farhanwadia/EEGClassification/Nov 2020 Filtered Data/5s/Images/Full Length FFTs/SD_T1 Open (valve) - FFT.png

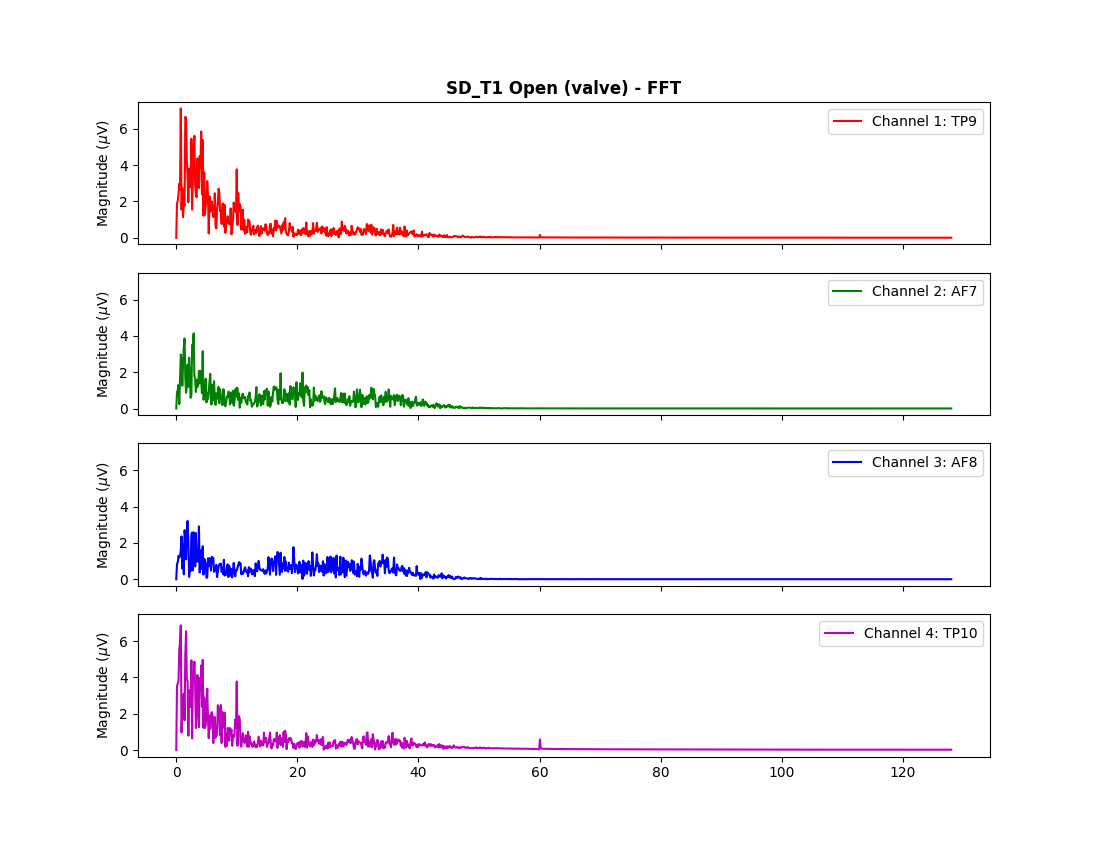
Nov 2020 Filtered Data/5s/Images/Full Length FFTs/SD_T1 Open (valve) - FFT.png
