farhanwadia/EEGClassification/Nov 2020 Filtered Data/5s/Images/Full Length FFTs/SD_T60 Close (valve) - FFT.png

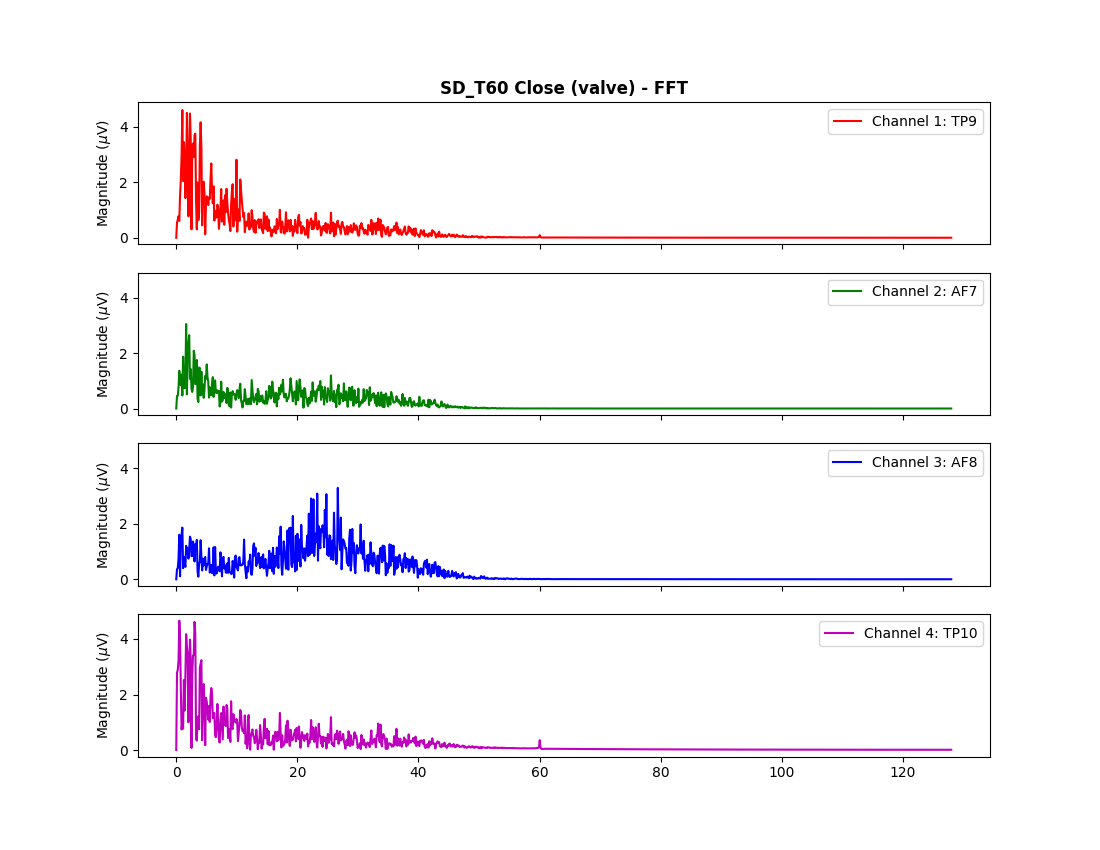
Nov 2020 Filtered Data/5s/Images/Full Length FFTs/SD_T60 Close (valve) - FFT.png
