farhanwadia/EEGClassification/Nov 2020 Filtered Data/5s/Images/ICA Images/AZ_T10 Open (valve) ICA.png

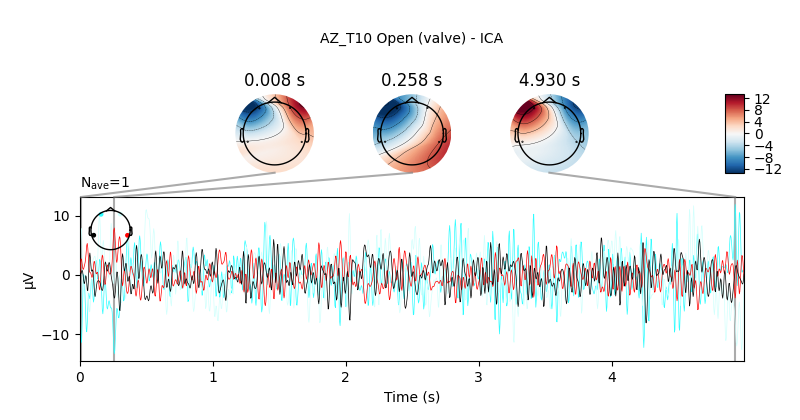
Nov 2020 Filtered Data/5s/Images/ICA Images/AZ_T10 Open (valve) ICA.png
