farhanwadia/EEGClassification/Nov 2020 Filtered Data/5s/Images/ICA Images/AZ_T17 Close (valve) ICA.png

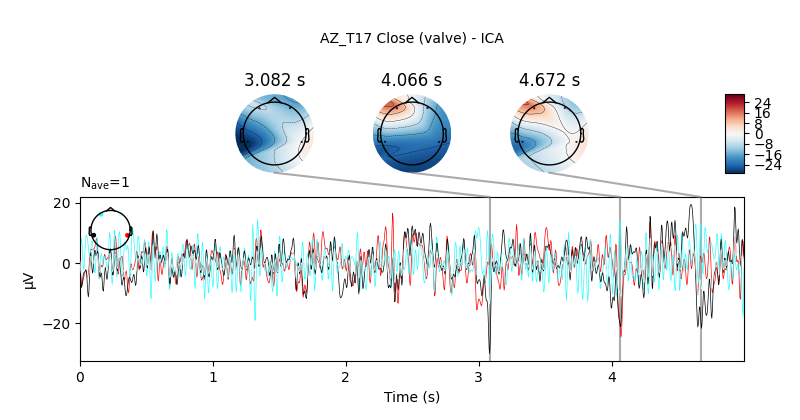
Nov 2020 Filtered Data/5s/Images/ICA Images/AZ_T17 Close (valve) ICA.png
