farhanwadia/EEGClassification/Nov 2020 Filtered Data/5s/Images/ICA Images/CJ_T1 Open (valve) ICA.png

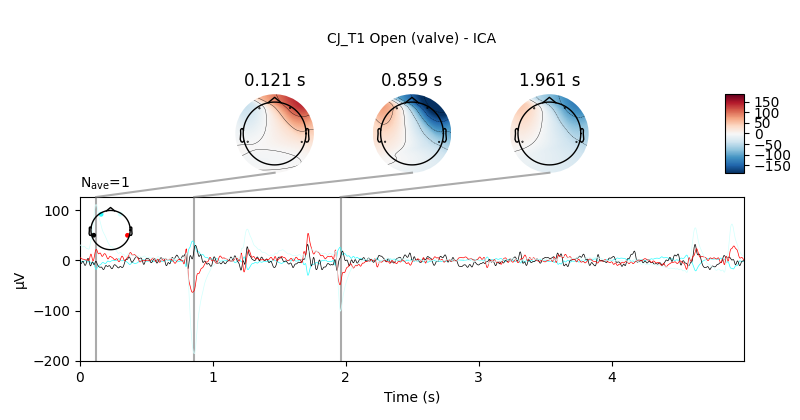
Nov 2020 Filtered Data/5s/Images/ICA Images/CJ_T1 Open (valve) ICA.png
