farhanwadia/EEGClassification/Nov 2020 Filtered Data/5s/Images/ICA Images/CJ_T15 Close (valve) ICA.png

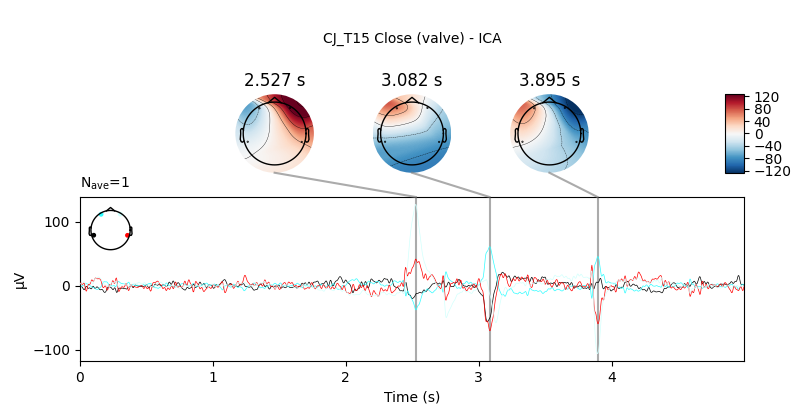
Nov 2020 Filtered Data/5s/Images/ICA Images/CJ_T15 Close (valve) ICA.png
