farhanwadia/EEGClassification/Nov 2020 Filtered Data/5s/Images/ICA Images/FW_T46 Close (valve) ICA.png

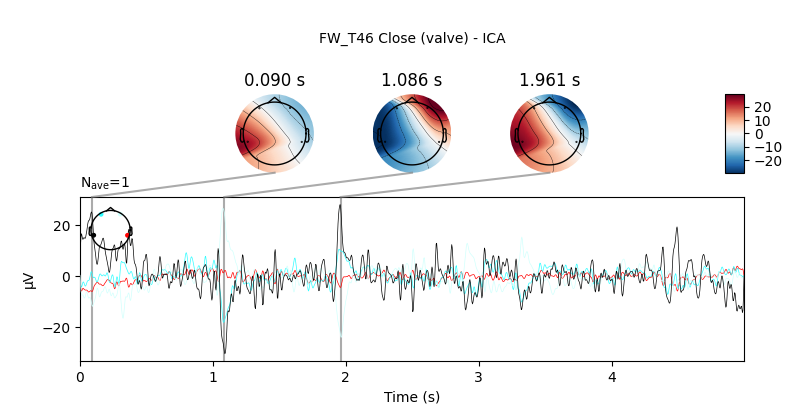
Nov 2020 Filtered Data/5s/Images/ICA Images/FW_T46 Close (valve) ICA.png
