farhanwadia/EEGClassification/Nov 2020 Filtered Data/5s/Images/ICA Images/FW_T76 Close (valve) ICA.png

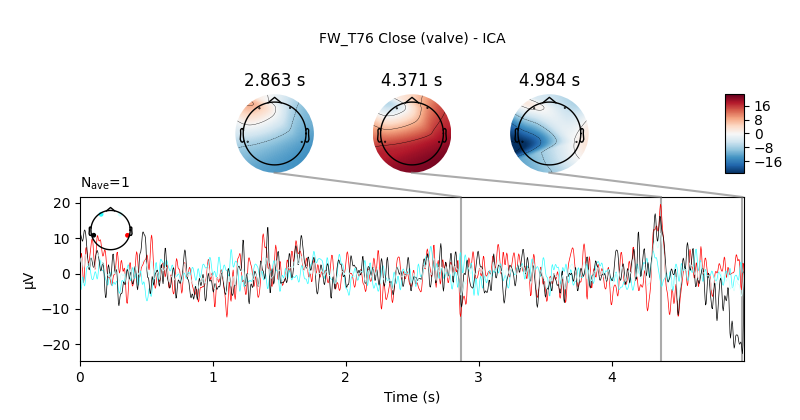
Nov 2020 Filtered Data/5s/Images/ICA Images/FW_T76 Close (valve) ICA.png
