farhanwadia/EEGClassification/Nov 2020 Filtered Data/5s/Images/ICA Images/SD_T7 Open (valve)_(2) ICA.png

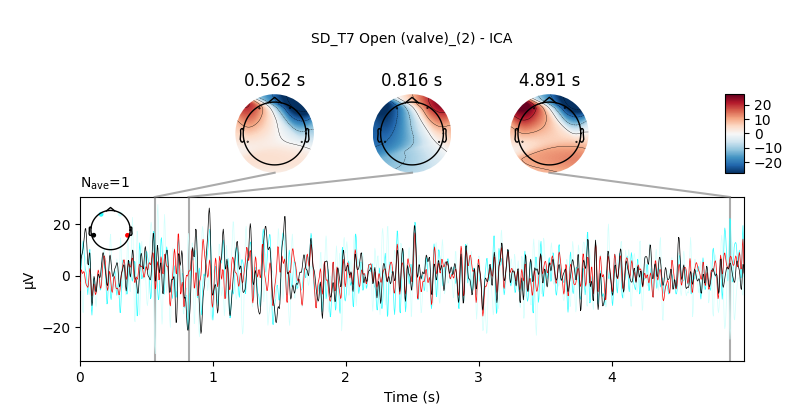
Nov 2020 Filtered Data/5s/Images/ICA Images/SD_T7 Open (valve)_(2) ICA.png
