farhanwadia/EEGClassification/Nov 2020 Filtered Data/5s/Images/ICA Images/SD_T11 Close (valve)_(1) ICA.png

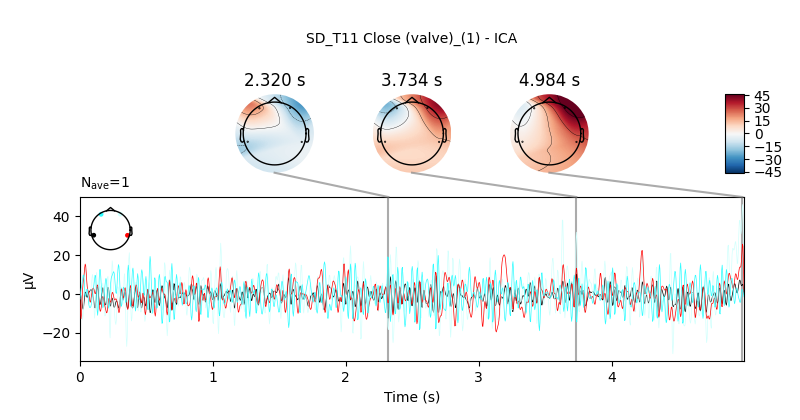
Nov 2020 Filtered Data/5s/Images/ICA Images/SD_T11 Close (valve)_(1) ICA.png
