farhanwadia/EEGClassification/Nov 2020 Filtered Data/5s/Images/ICA Images/SD_T21 Open (valve) ICA.png

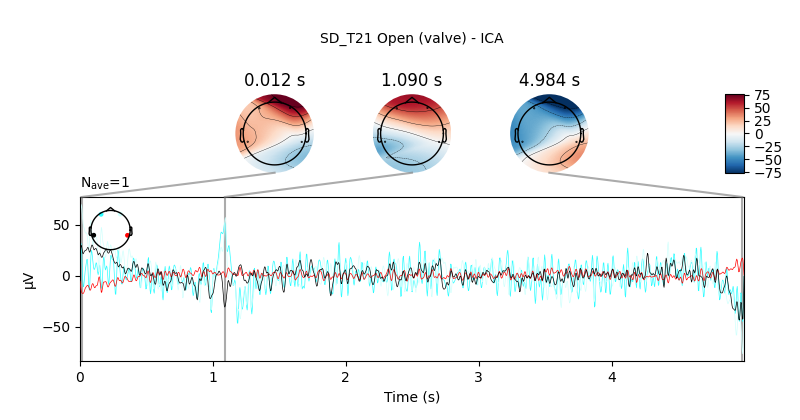
Nov 2020 Filtered Data/5s/Images/ICA Images/SD_T21 Open (valve) ICA.png
