farhanwadia/EEGClassification/Nov 2020 Filtered Data/5s/Images/ICA Images/SD_T22 Close (valve) ICA.png

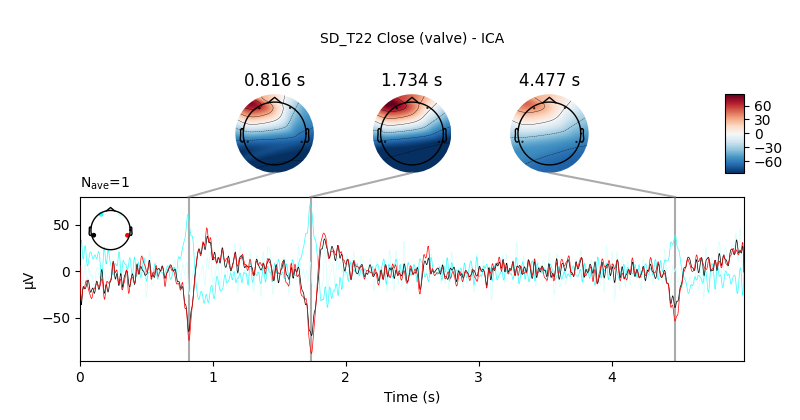
Nov 2020 Filtered Data/5s/Images/ICA Images/SD_T22 Close (valve) ICA.png
