farhanwadia/EEGClassification/Nov 2020 Filtered Data/5s/Images/ICA Images/SD_T28 Close (valve) ICA.png

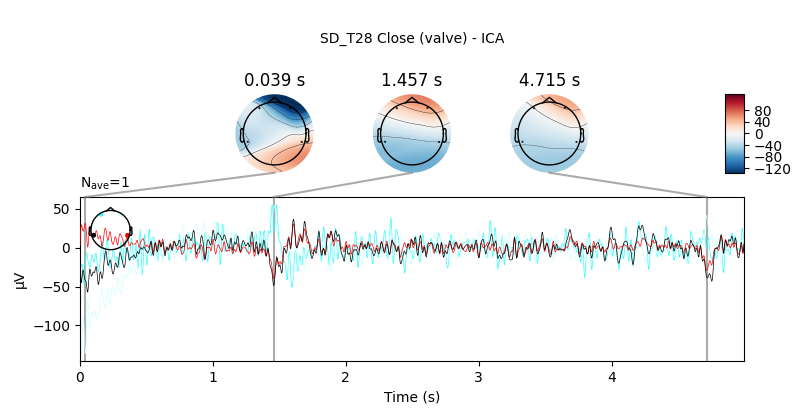
Nov 2020 Filtered Data/5s/Images/ICA Images/SD_T28 Close (valve) ICA.png
