farhanwadia/EEGClassification/Prototype and Final Design CAD Assemblies/Parts/Power Diode 1N4001.step

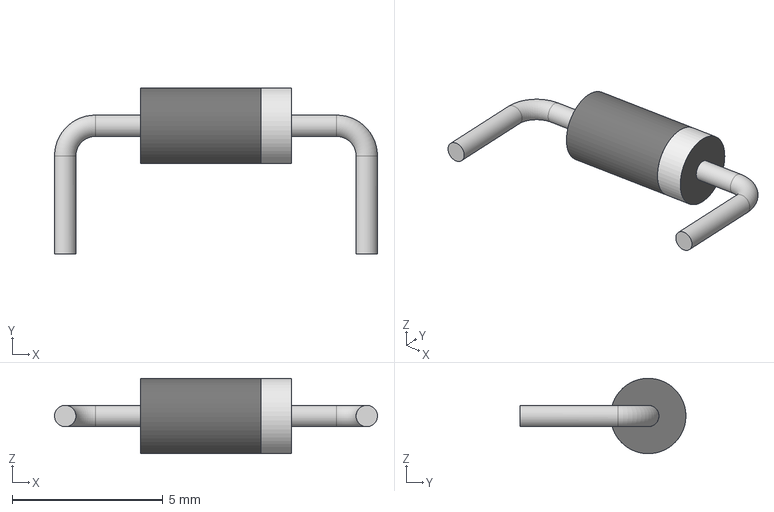
[picture p157: CAD file, 2021-03-26]
Prototype and Final Design CAD Assemblies/Parts/Power Diode 1N4001.step
10.7 x 5.50 x 2.50 mm
