farhanwadia/EEGClassification/Prototype and Final Design CAD Assemblies/Parts/Solenoid.SLDPRT

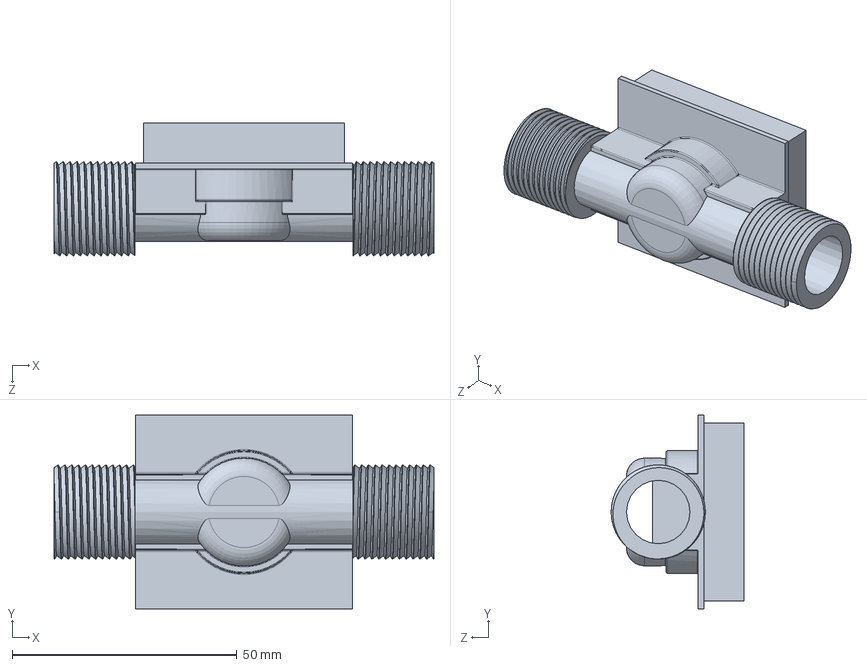
[picture p158: CAD file, 2021-03-26]
Prototype and Final Design CAD Assemblies/Parts/Solenoid.SLDPRT
84.6 x 43.2 x 29.5 mm
