farhanwadia/EEGClassification/Prototype and Final Design CAD Assemblies/Parts/cylinder.SLDPRT

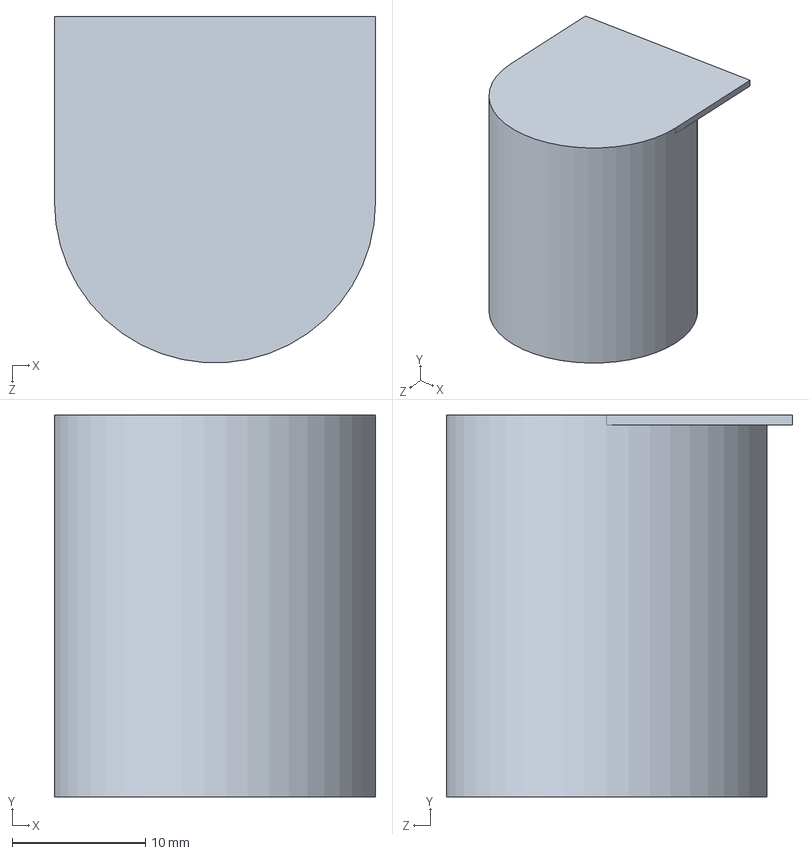
[picture p159: CAD file, 2021-03-26]
Prototype and Final Design CAD Assemblies/Parts/cylinder.SLDPRT
24.1 x 28.7 x 26.0 mm
