farhanwadia/EEGClassification/Prototype and Final Design CAD Assemblies/Parts/LEAD.SLDPRT

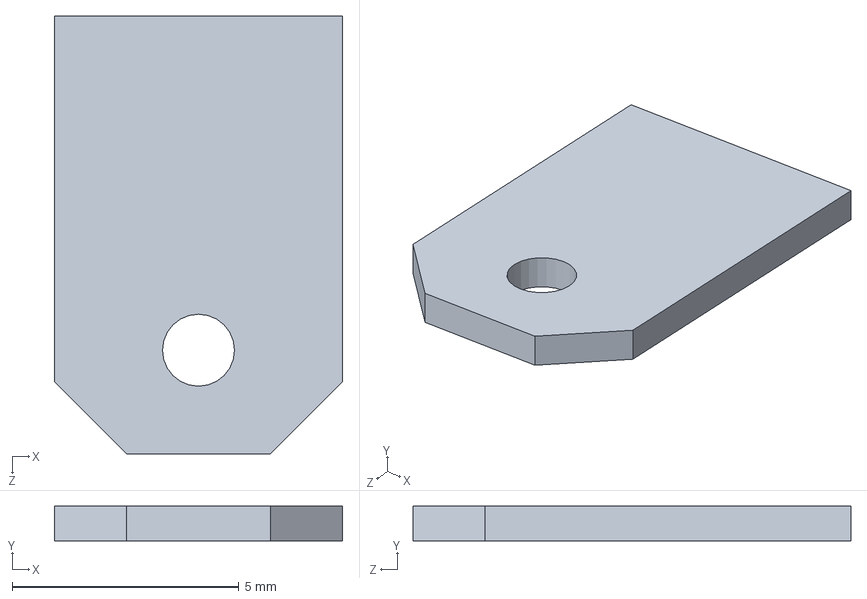
[picture p160: CAD file, 2021-03-26]
Prototype and Final Design CAD Assemblies/Parts/LEAD.SLDPRT
6.35 x 0.762 x 9.65 mm
