farhanwadia/EEGClassification/Prototype and Final Design CAD Assemblies/Parts/LED 3mm, Red, Thru-hole, Right Angle PCB 2.stp

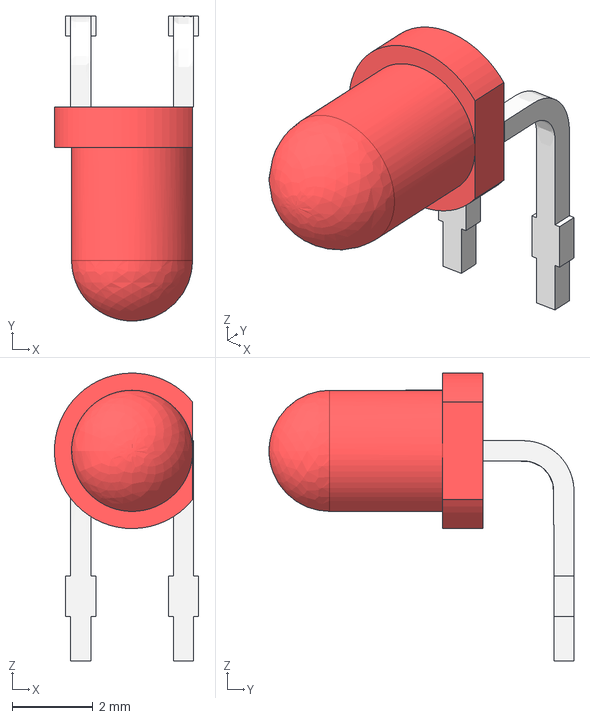
[picture p161: CAD file, 2021-03-26]
Prototype and Final Design CAD Assemblies/Parts/LED 3mm, Red, Thru-hole, Right Angle PCB 2.stp
3.57 x 7.55 x 7.12 mm
